wilson-malone/Arduino-Weather-Station/Pictures/PXL_20240608_183827319.jpg

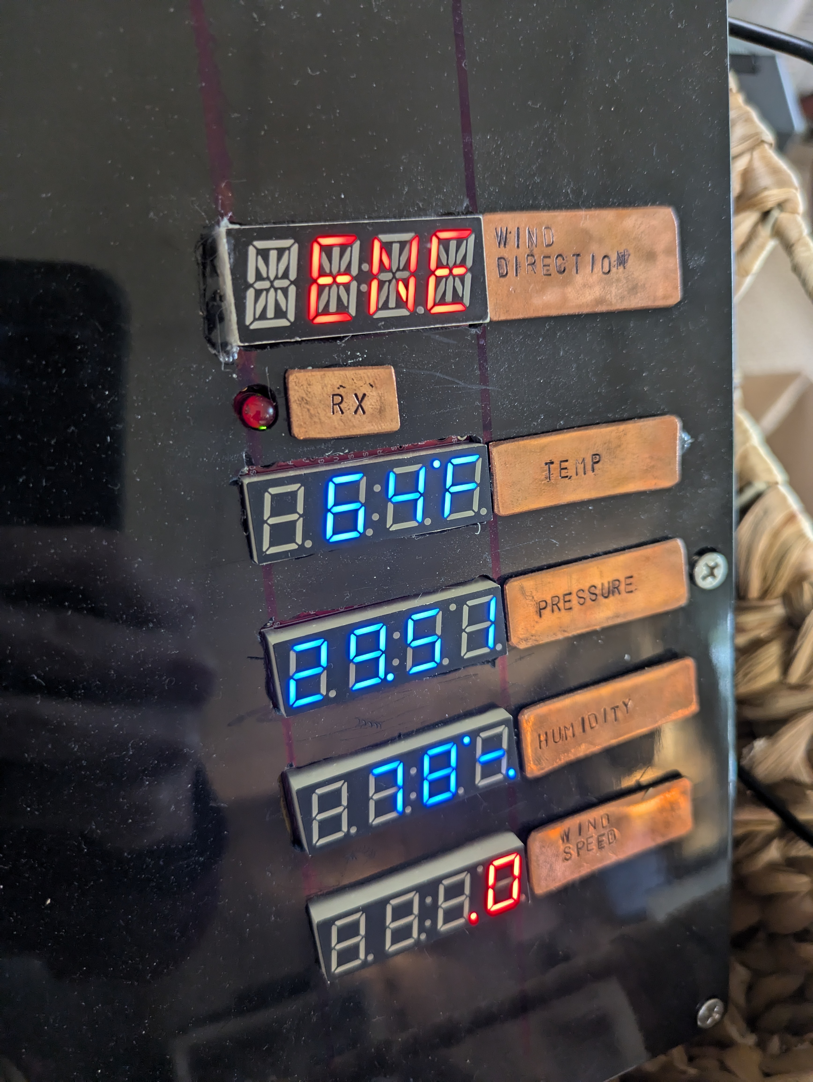
Pictures/PXL_20240608_183827319.jpg
