wilson-malone/Arduino-Weather-Station/Pictures/PXL_20240707_150827254.jpg

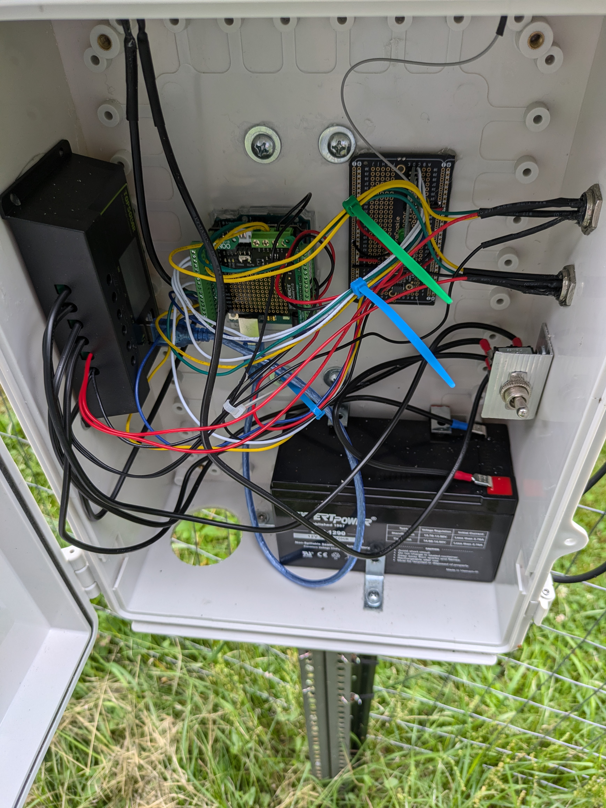
Pictures/PXL_20240707_150827254.jpg
