wilson-malone/Arduino-Weather-Station/Pictures/PXL_20260729_204759346[1].jpg

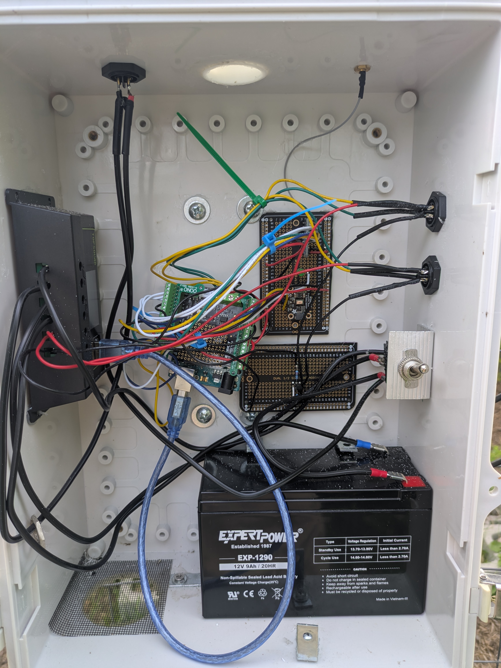
Pictures/PXL_20260729_204759346[1].jpg
