wilson-malone/Arduino-Weather-Station/Schematics/7 segment displays/7sd_bb.png

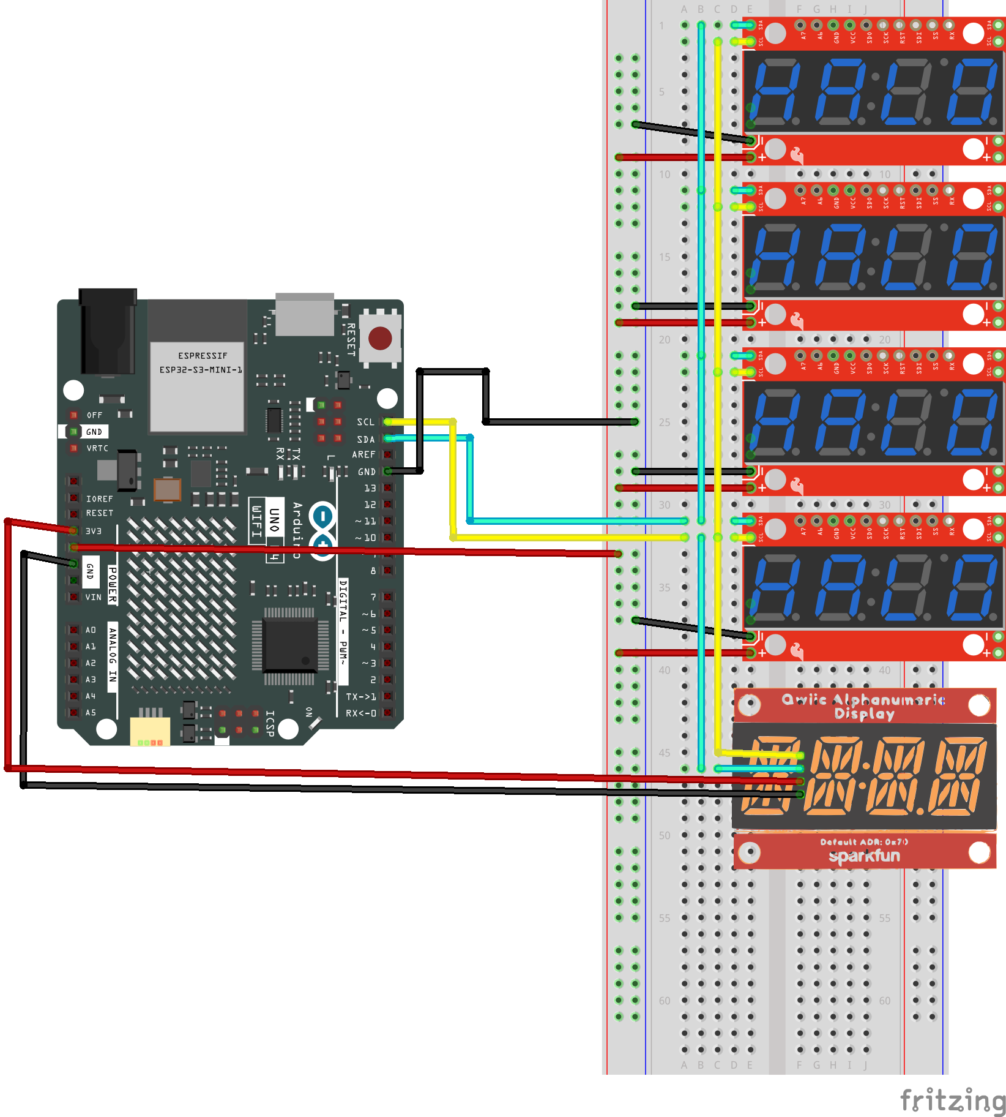
Schematics/7 segment displays/7sd_bb.png
