wilson-malone/Arduino-Weather-Station/Schematics/Automatic Power Switching/Automatic Power switch_schem.png

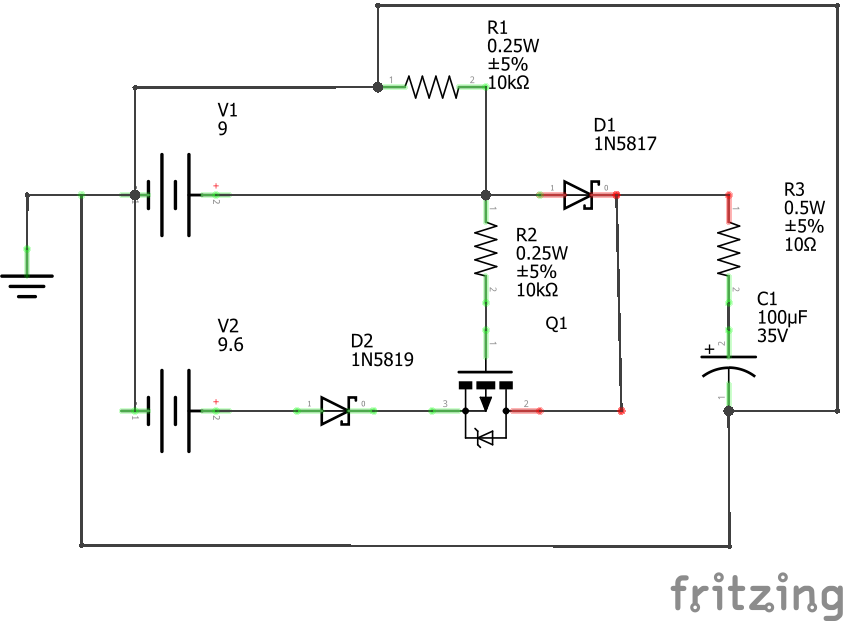
Schematics/Automatic Power Switching/Automatic Power switch_schem.png
