wilson-malone/Arduino-Weather-Station/Schematics/Blinking LED/Transistor_bb.png

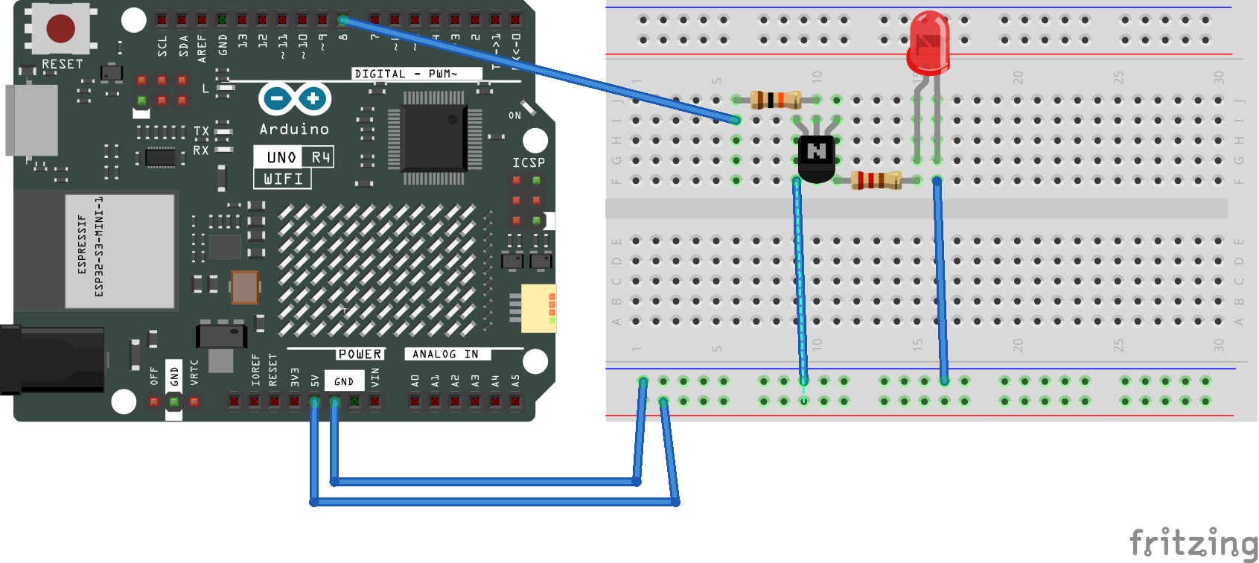
Schematics/Blinking LED/Transistor_bb.png
