wilson-malone/Arduino-Weather-Station/Schematics/Power client/client power_schem.png

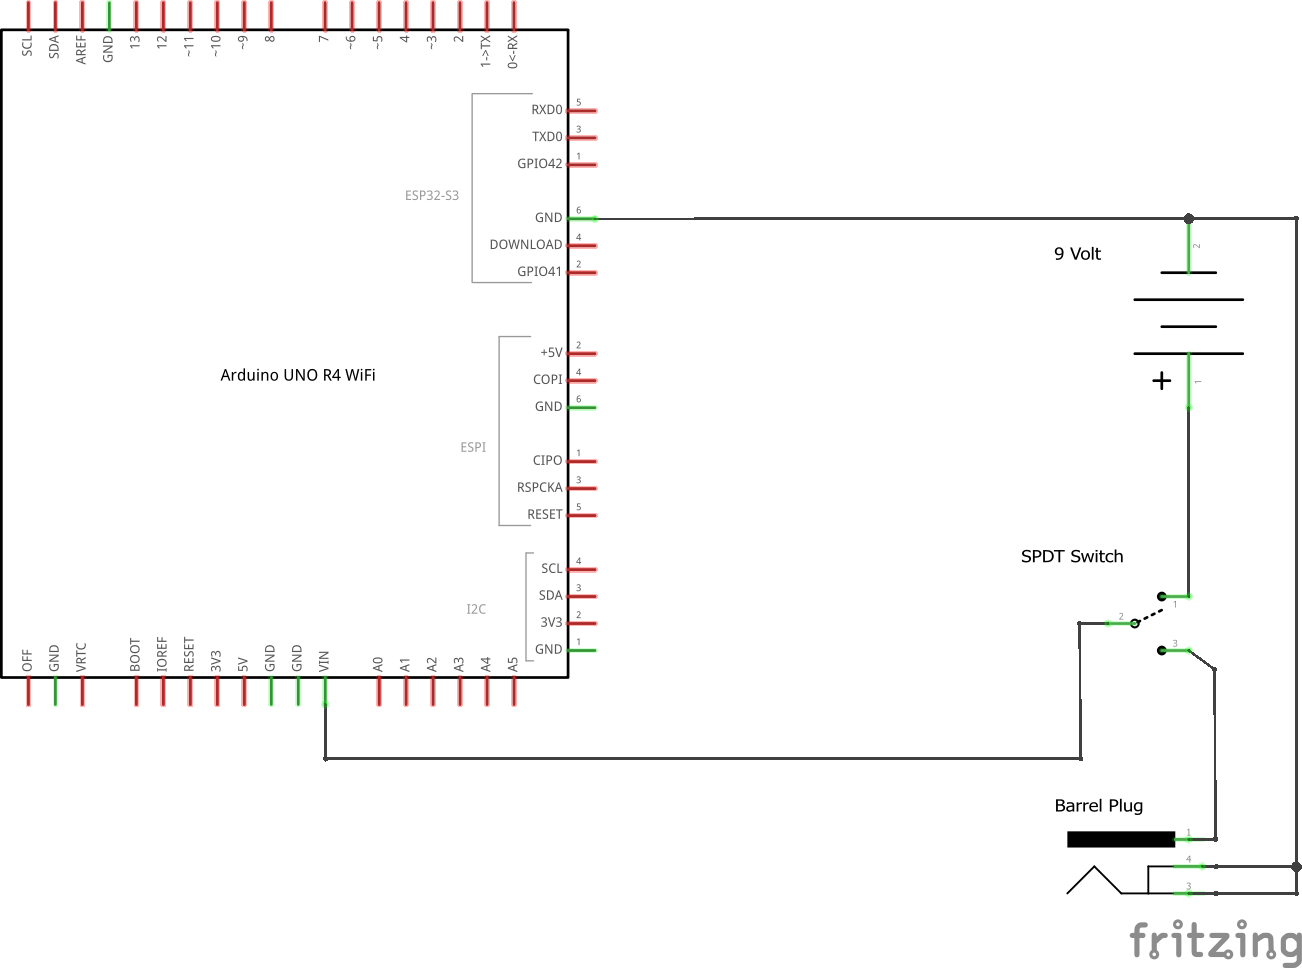
Schematics/Power client/client power_schem.png
