wilson-malone/Arduino-Weather-Station/Schematics/Radio/RFM69HCW_bb.png

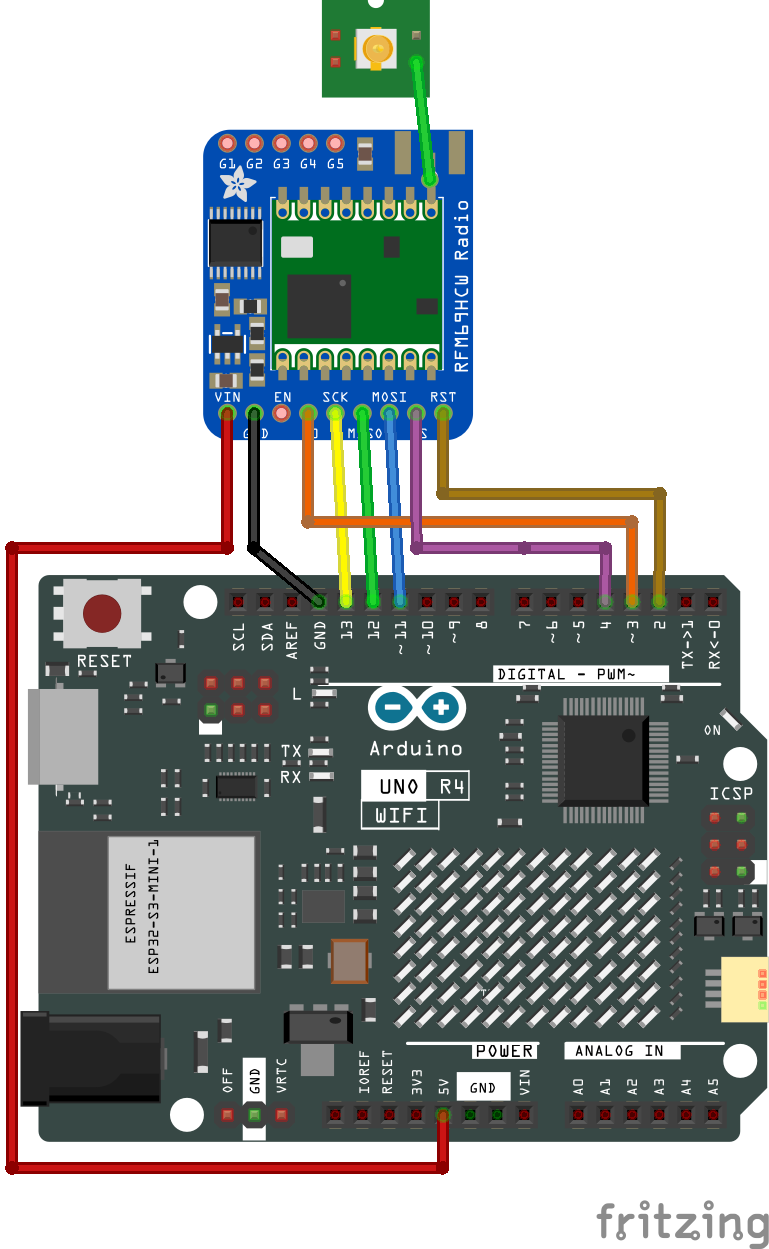
Schematics/Radio/RFM69HCW_bb.png
