wilson-malone/Arduino-Weather-Station/Schematics/Radio/RFM69HCW_schem.png

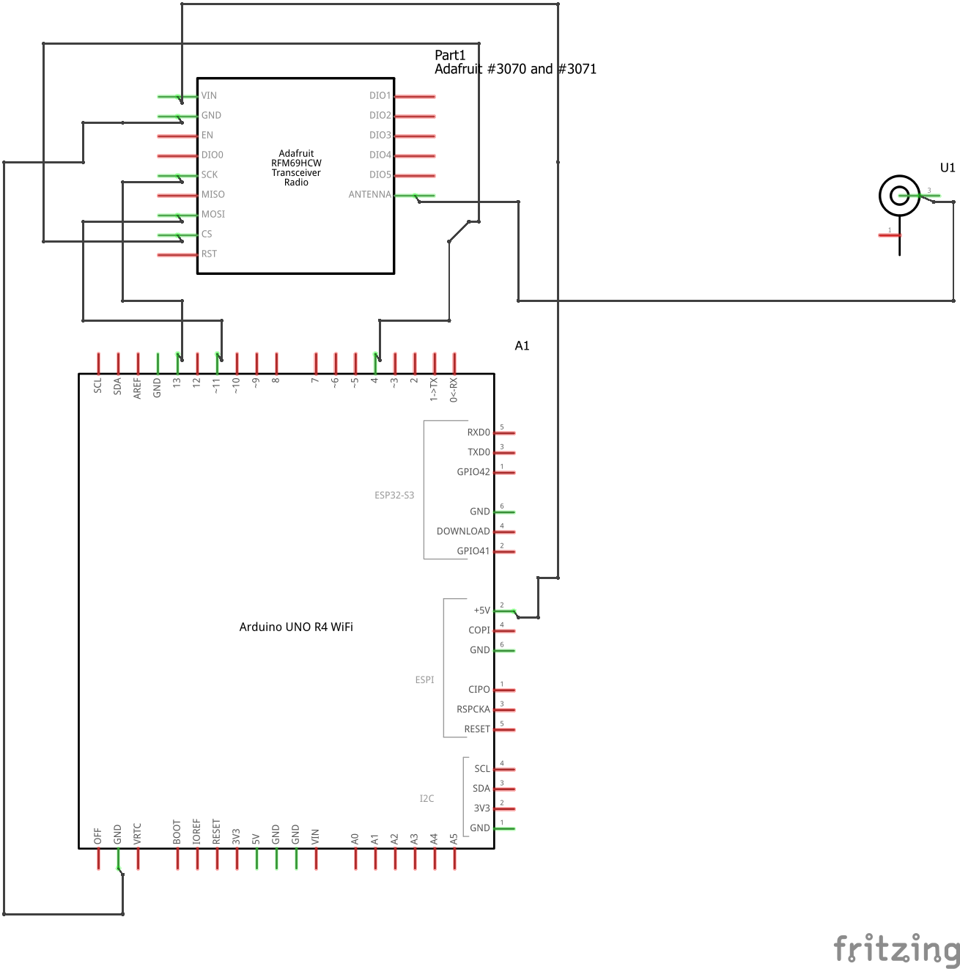
Schematics/Radio/RFM69HCW_schem.png
