wilson-malone/Arduino-Weather-Station/Schematics/Vane/Screenshot 2024-06-10 183025.png

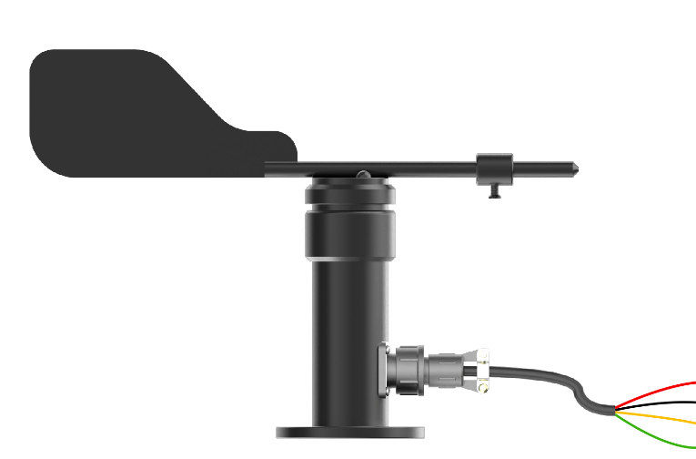
Schematics/Vane/Screenshot 2024-06-10 183025.png
