wilson-malone/Arduino-Weather-Station/Schematics/Automatic Power Switching/Draft1.asc

M2: nmos; SQS482EN
R1: res; 10k
R2: res; 100
V1: voltage; 12
V3: voltage; PULSE(0 5 .25 .001 .001 .25 .5)
Named nets: 0
.tran 2
