wilson-malone/Arduino-Weather-Station/Schematics/Automatic Power Switching/draft2.asc

C1: cap; 100µF
D1: schottky; 1N5819
D2: schottky; 1N5819
D3: schottky; 1N5819
D4: schottky; 1N5819
M1: pmos; irf9310pbf
R1: res; 80
R2: res; 10k
R4: res; 10k
R5: res; 100
V1: voltage; PULSE(0 9 .5s 1ms 1ms .5s 1)
V2: voltage; 9.6
Named nets: 0
.tran 4
.LIB irf9310pbf.spi
